Abhey-05/Thermal-Camera/Codes and Gerber files/Codes/BootAnimation.h

//
// wlecome-ezgif.com-video-to-gif-converter
// Data size = 90904 bytes
//
// GIF, Compression=LZW, Size: 320 x 320, 8-Bpp
// 30 frames
//
// for non-Arduino builds...
#ifndef PROGMEM
#define PROGMEM
#endif
const uint8_t BootAnimationIMG[] PROGMEM = {
	0x47,0x49,0x46,0x38,0x39,0x61,0x40,0x01,0x40,0x01,0xf7,0xff,0x31,0x00,0x00,0x00,
	0x01,0x00,0x01,0x01,0x00,0x02,0x02,0x00,0x00,0x03,0x01,0x01,0x04,0x03,0x02,0x05,
	0x00,0x00,0x07,0x00,0x00,0x08,0x04,0x03,0x09,0x00,0x00,0x0c,0x00,0x00,0x0d,0x08,
	0x06,0x10,0x00,0x00,0x13,0x0f,0x0d,0x15,0x00,0x00,0x18,0x02,0x00,0x1a,0x14,0x12,
	0x1d,0x00,0x00,0x1d,0x1f,0x41,0x1f,0x06,0x00,0x1f,0x1c,0x1c,0x22,0x22,0x22,0x24,
	0x26,0x3c,0x25,0x25,0x27,0x25,0x26,0x28,0x26,0x00,0x00,0x26,0x26,0x27,0x26,0x27,
	0x29,0x27,0x0a,0x01,0x27,0x24,0x23,0x27,0x27,0x27,0x2c,0x2c,0x33,0x2d,0x01,0x00,
	0x2e,0x26,0x23,0x31,0x2c,0x76,0x31,0x31,0x31,0x32,0x0b,0x01,0x35,0x00,0x00,0x37,
	0x35,0x61,0x3c,0x00,0x00,0x3c,0x0f,0x02,0x3e,0x1b,0x0c,0x41,0x2e,0x25,0x43,0x3e,
	0x87,0x44,0x42,0x70,0x44,0x44,0x4b,0x45,0x01,0x00,0x46,0x3b,0x36,0x47,0x12,0x00,
	0x4e,0x49,0x92,0x4e,0x4e,0x54,0x50,0x04,0x00,0x51,0x16,0x01,0x51,0x4e,0x7f,0x52,
	0x1c,0x07,0x56,0x51,0xa0,0x57,0x57,0x57,0x58,0x04,0x00,0x58,0x2b,0x18,0x58,0x55,
	0x94,0x59,0x59,0x69,0x5b,0x18,0x01,0x5b,0x58,0x89,0x60,0x02,0x00,0x60,0x19,0x00,
	0x60,0x3b,0x2a,0x60,0x5e,0x5d,0x62,0x0c,0x00,0x62,0x5e,0xa3,0x64,0x61,0x95,0x67,
	0x21,0x02,0x67,0x44,0x35,0x69,0x69,0x6f,0x6a,0x09,0x00,0x6b,0x66,0xac,0x6b,0x69,
	0x8c,0x6c,0x69,0x9d,0x6f,0x6f,0x6f,0x72,0x22,0x00,0x73,0x16,0x00,0x75,0x27,0x06,
	0x76,0x72,0xb5,0x78,0x4f,0x3d,0x78,0x76,0x9f,0x79,0x76,0xa8,0x7a,0x7a,0x7a,0x7b,
	0x7a,0x94,0x7f,0x30,0x0d,0x82,0x7e,0xc1,0x84,0x12,0x00,0x85,0x81,0xb4,0x86,0x85,
	0xa6,0x87,0x87,0x8a,0x89,0x27,0x00,0x8b,0x3b,0x17,0x8c,0x6a,0x5b,0x8c,0x79,0x72,
	0x8d,0x89,0xc8,0x8e,0x8b,0xbd,0x8f,0x8d,0xb4,0x92,0x17,0x00,0x92,0x2d,0x02,0x95,
	0x48,0x25,0x95,0x93,0xa4,0x96,0x96,0x97,0x97,0x59,0x49,0x99,0x95,0xd0,0x9a,0x98,
	0xbe,0x9c,0x1d,0x00,0x9f,0x31,0x05,0xa0,0x84,0x7a,0xa1,0x9d,0xe6,0xa1,0xa1,0xa2,
	0xa3,0x69,0x5b,0xa4,0xa1,0xd4,0xa4,0xa2,0xc9,0xa5,0x4e,0x27,0xa6,0x36,0x04,0xa6,
	0xa4,0xb3,0xa9,0x56,0x31,0xaa,0xa7,0xe0,0xac,0xa9,0xa7,0xae,0x3d,0x0a,0xae,0xac,
	0xcb,0xaf,0x24,0x00,0xb0,0xb0,0xb1,0xb4,0x60,0x3c,0xb4,0xb0,0xed,0xb5,0xb4,0xd4,
	0xb6,0x31,0x00,0xba,0x43,0x0f,0xbb,0xbc,0xbf,0xbd,0xba,0xef,0xc0,0x4f,0x1c,0xc0,
	0xbf,0xda,0xc1,0x37,0x01,0xc1,0x5b,0x32,0xc3,0x43,0x38,0xc6,0x6c,0x58,0xc6,0xc3,
	0xf4,0xc6,0xc6,0xc8,0xc7,0x45,0x09,0xc8,0xc6,0xe2,0xc9,0x58,0x26,0xca,0x56,0x3c,
	0xcd,0x64,0x45,0xce,0x83,0x70,0xce,0xcd,0xea,0xcf,0x3c,0x04,0xcf,0xcc,0xfc,0xd0,
	0x38,0x2e,0xd1,0xd2,0xd4,0xd2,0x7f,0x3d,0xd3,0x4f,0x20,0xd4,0x5f,0x3f,0xd7,0x8e,
	0x52,0xd9,0x4a,0x18,0xd9,0x56,0x35,0xd9,0xc1,0x8e,0xd9,0xd7,0xf9,0xda,0x2f,0x24,
	0xda,0x50,0x2a,0xda,0xa5,0x46,0xdb,0xa6,0x4c,0xdc,0x2e,0x25,0xdc,0x53,0x16,0xdc,
	0xdc,0xdf,0xdd,0x2e,0x25,0xdd,0x86,0x3a,0xde,0x3d,0x0a,0xde,0x6f,0x66,0xdf,0x4e,
	0x2f,0xdf,0x7c,0x23,0xe0,0x4e,0x25,0xe0,0x4e,0x26,0xe1,0x4e,0x25,0xe1,0x79,0x35,
	0xe1,0x7c,0x25,0xe1,0x8c,0x7a,0xe2,0x4a,0x0a,0xe2,0x92,0x54,0xe3,0x4d,0x1d,0xe3,
	0x50,0x13,0xe3,0x8a,0x69,0xe4,0x7b,0x27,0xe4,0xa4,0x90,0xe5,0xe3,0xfe,0xe6,0x7a,
	0x24,0xe6,0x7a,0x26,0xe6,0x7b,0x25,0xe6,0x94,0x56,0xe6,0xe6,0xf5,0xe7,0x5f,0x34,
	0xe7,0x7b,0x25,0xe7,0xe6,0xe8,0xe8,0x7c,0x25,0xe8,0x9b,0x27,0xe9,0x4c,0x05,0xeb,
	0x86,0x5e,0xeb,0xa3,0x1d,0xeb,0xa3,0x1e,0xeb,0xd0,0xc5,0xeb,0xe6,0xe0,0xec,0x88,
	0x5f,0xec,0xb8,0xa4,0xed,0x4d,0x05,0xed,0x5f,0x13,0xed,0xb3,0x6c,0xed,0xcf,0x46,
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
